BrunoFA-git/wideband/hardware/simulation/NernstSenseModel.asc

C1: cap; 100n
C2: cap; 1µ
C3: cap; 1n
L1: ind; 2µ
L2: ind; 2µ
L3: ind; 2µ
L4: ind; 2µ
R1: res; 150
R2: res; 300
R3: res; 22k
R4: res; 10k
R5: res; 95
R6: res; 61.9
R7: res; 10k
R8: res; 30k
R9: res; 30k
R10: res; 10k
R11: res; 10k
R12: res; 10k
R13: res; 10k
R14: res; 10k
R15: res; 3.3k
R16: res; 3.3k
R17: res; 10
U1: opamp
U2: AD822
U3: AD822
U4: AD822
U5: AD822
V1: voltage; 1.65
V2: voltage; 0.45
V3: voltage; 3.3
V4: voltage; PULSE(0 3.3 10m 100n 100n 250u 500u)
V5: voltage; 0.2
Named nets: 0, Un, Ip, Vm, nernst_sense, vcc, Vm_ext
.tran 0 30m 0 100n
.lib opamp.sub
Sensor Model
