BrunoFA-git/wideband/hardware/simulation/PumpDriverModel.asc

C1: cap; 33n
C4: cap; 100n
R1: res; 68k
R2: res; 68k
R3: res; 10k
R4: res; 10k
R5: res; 47
R6: res; 3.3k
R7: res; 95
R8: res; 61.9
R9: res; 10
R10: res; 10k
R11: res; 10k
R12: res; 100k
R13: res; 100k
U1: AD822
U2: AD822
U3: LT1720
V1: voltage; 1.65
V2: voltage; 0; AC 1
V3: voltage; 3.3
V4: voltage; PULSE(-0.3 0.3 5m 30n 30n 5m 10m)
V5: voltage; PULSE(0 3.3 0 5u 0 100n 5u)
V6: voltage; 1m
Named nets: 0, vcc, vm, sense_out, rtrim, ip, input
;.ac dec 400 10 1e7
PWM modulator - transient analysis
AC analysis
.dc V6 -5m 5m
Power Supply
Pump Current Sense
Pump Current Source
Sensor
